Acigap/SmartPlantCare/image/T-DISPLAY-S3.jpg

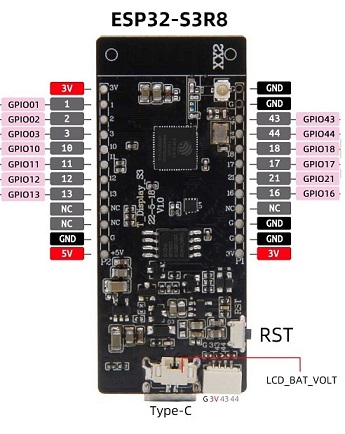
image/T-DISPLAY-S3.jpg
